TinyCircuits/TinyCircuits-Whisker-Joystick-AST1011/cad/Wireling_JOYSTICK_AST1011_REV2-DETAILED_DRAWING_COMPACT-PNG.png

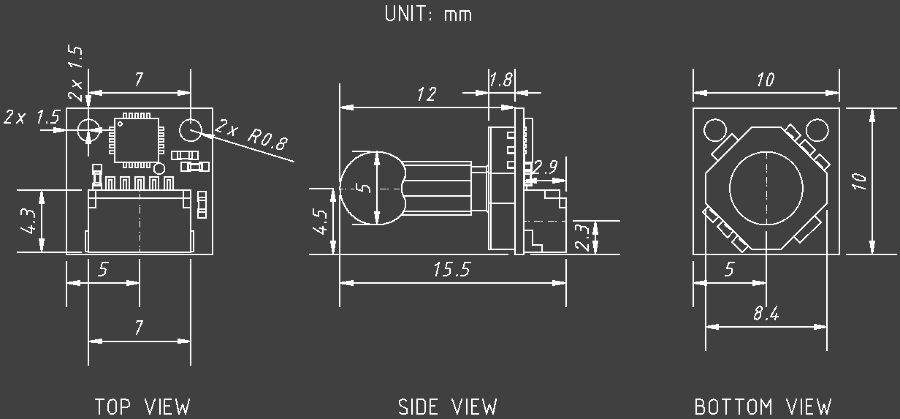
cad/Wireling_JOYSTICK_AST1011_REV2-DETAILED_DRAWING_COMPACT-PNG.png
