TinyCircuits/TinyCircuits-Whisker-Joystick-AST1011/images/AST1011-Product-Photo-04.png

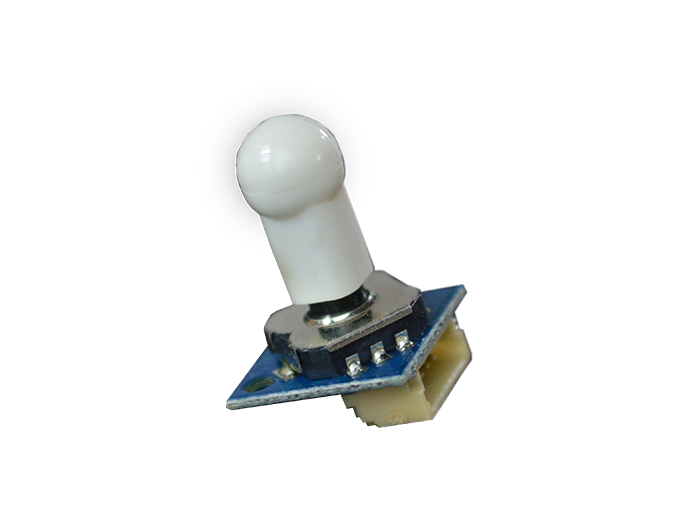
images/AST1011-Product-Photo-04.png
