TinyCircuits/TinyCircuits-Whisker-Joystick-AST1011/images/AST1011-Tutorial-Image-02.1.jpg

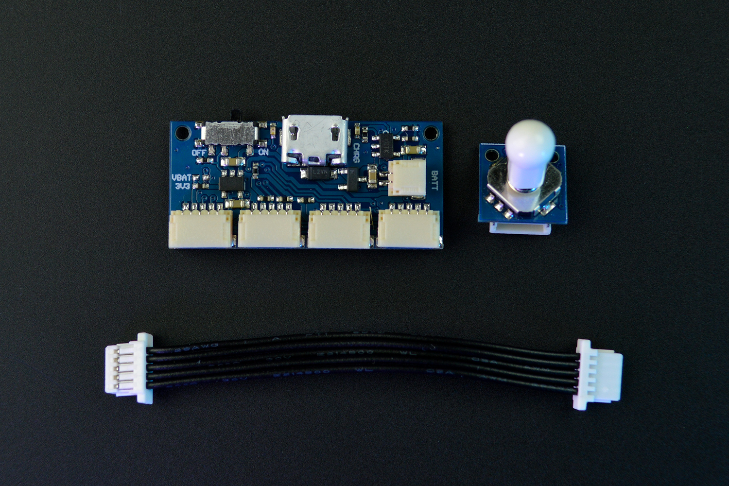
images/AST1011-Tutorial-Image-02.1.jpg
